microsoft/SmartKC-A-Smartphone-based-Corneal-Topographer/data/sample_images/kc_left.jpg

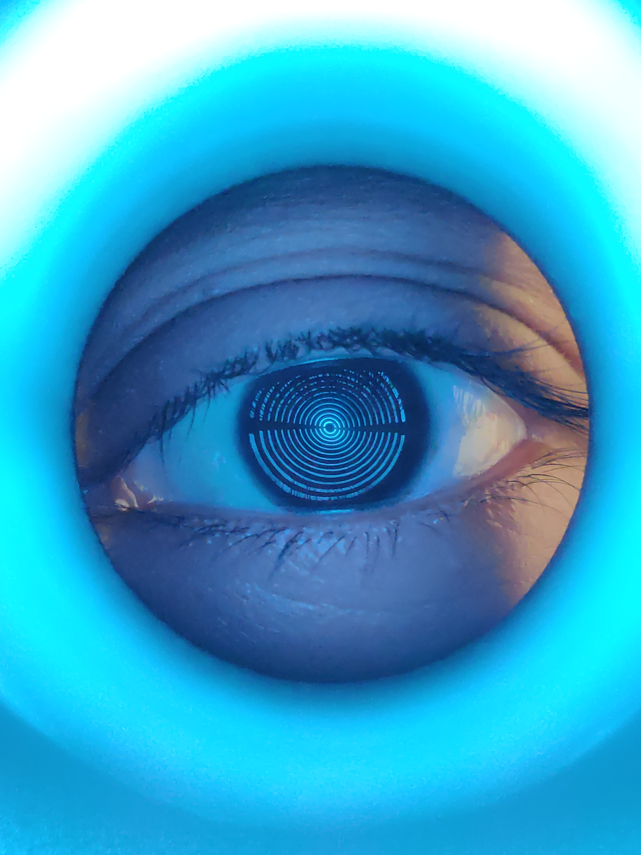
data/sample_images/kc_left.jpg
