microsoft/SmartKC-A-Smartphone-based-Corneal-Topographer/data/sample_images/kc_right.jpg

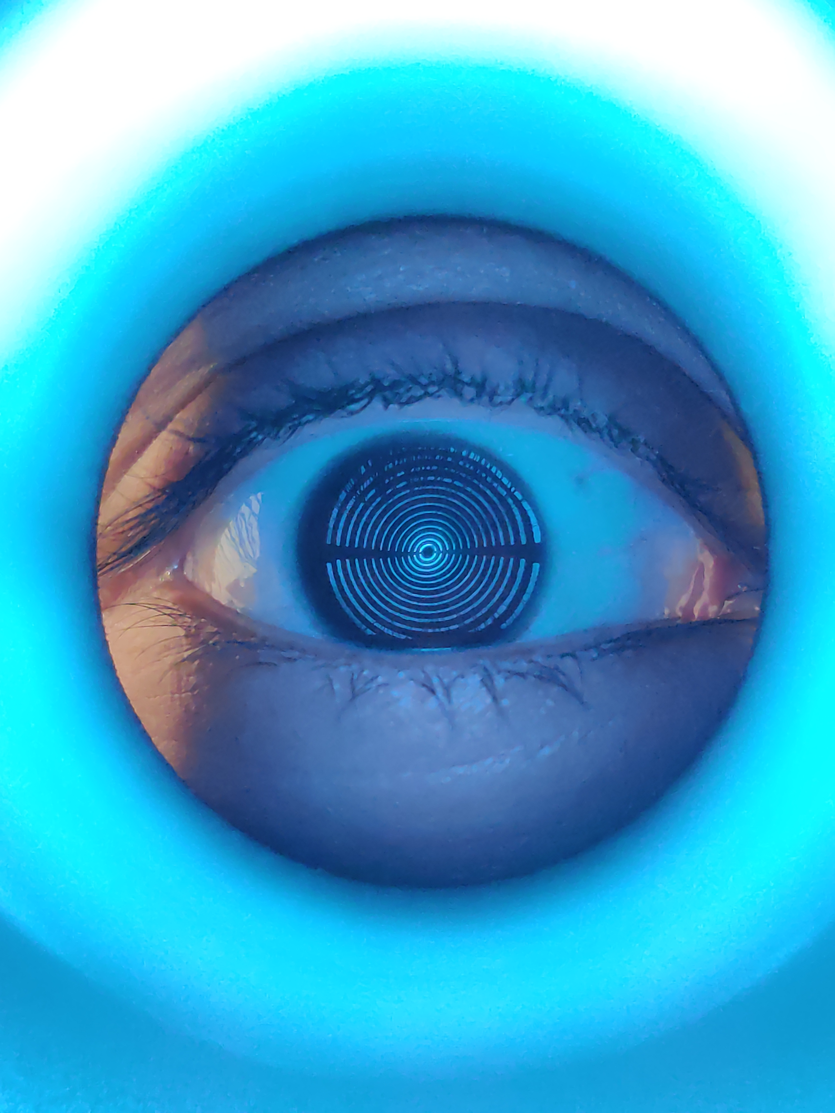
data/sample_images/kc_right.jpg
