microsoft/SmartKC-A-Smartphone-based-Corneal-Topographer/data/sample_images/nokc_left.jpg

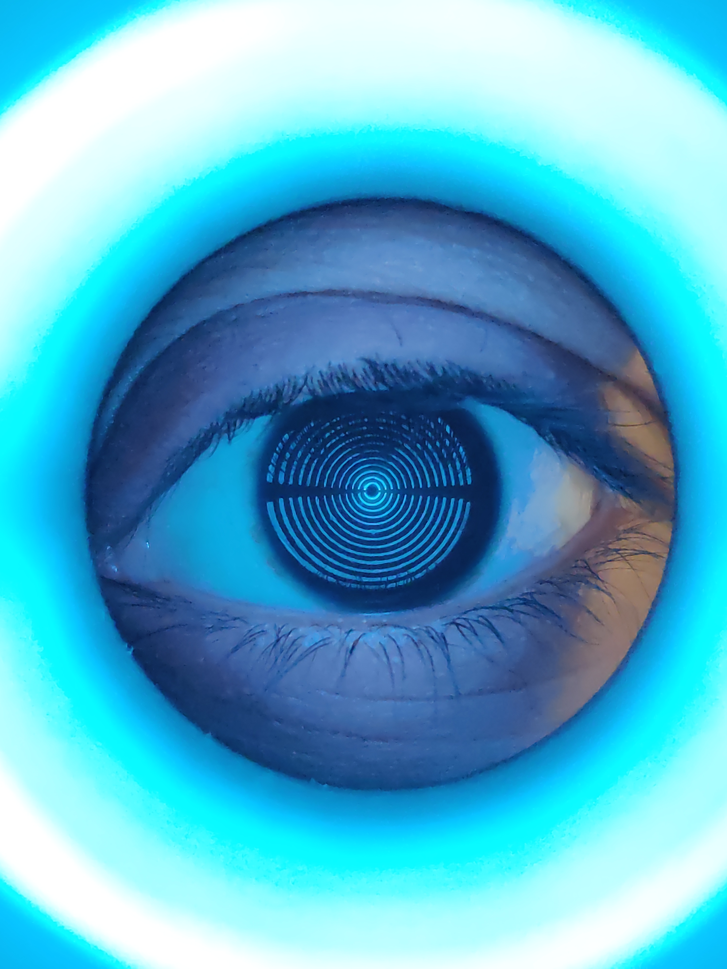
data/sample_images/nokc_left.jpg
