microsoft/SmartKC-A-Smartphone-based-Corneal-Topographer/data/sample_images/nokc_right.jpg

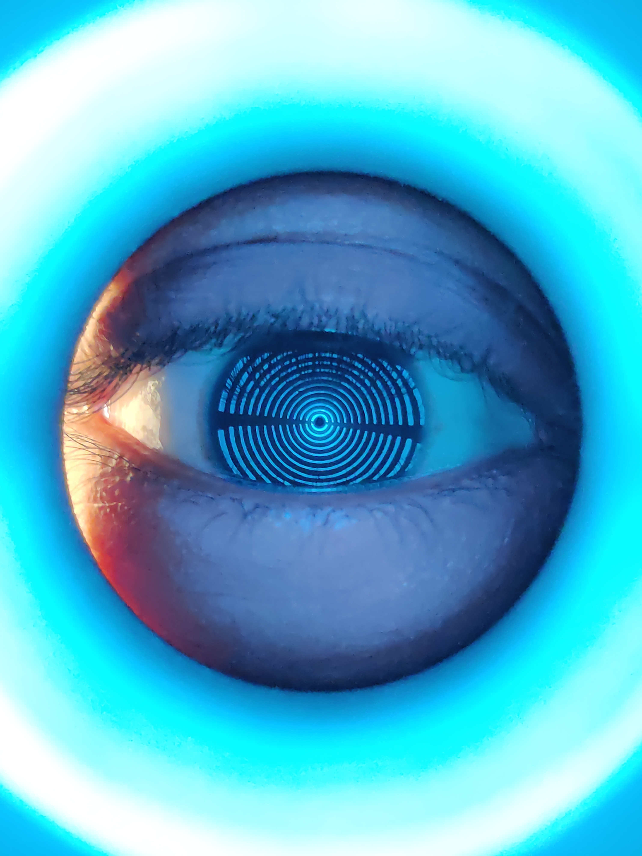
data/sample_images/nokc_right.jpg
