microsoft/SmartKC-A-Smartphone-based-Corneal-Topographer/data/sample_images_results/kc_left/kc_left_axialmap.png

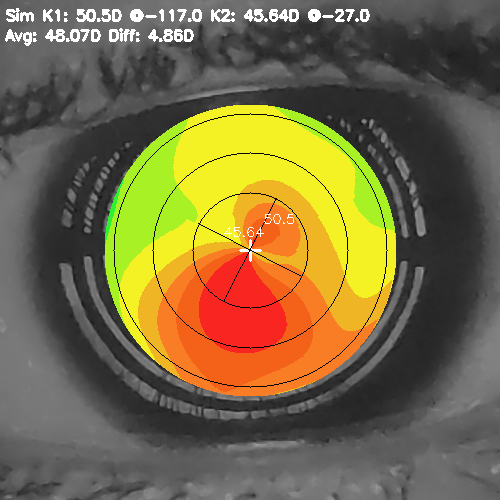
data/sample_images_results/kc_left/kc_left_axialmap.png
