microsoft/SmartKC-A-Smartphone-based-Corneal-Topographer/data/sample_images_results/kc_right/kc_right_tanmap.png

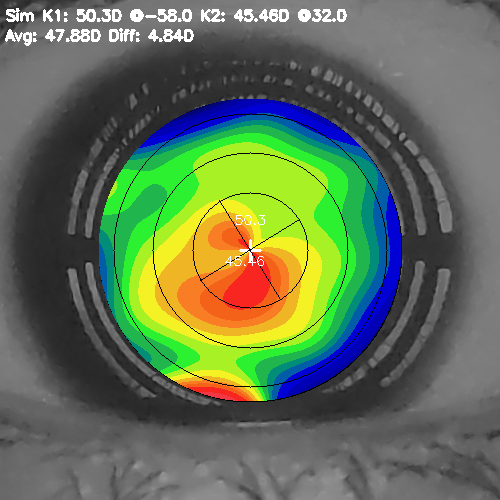
data/sample_images_results/kc_right/kc_right_tanmap.png
