microsoft/SmartKC-A-Smartphone-based-Corneal-Topographer/data/sample_images_results/nokc_left/nokc_left_axialmap.png

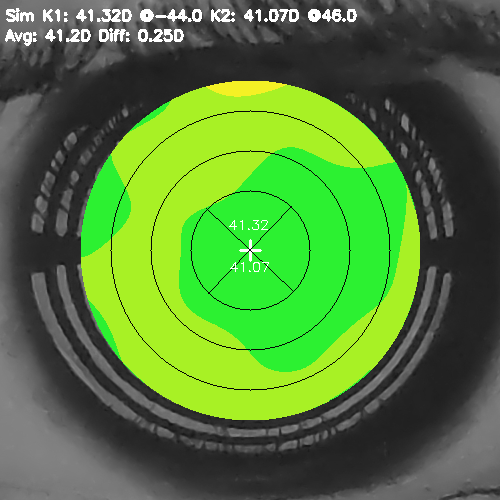
data/sample_images_results/nokc_left/nokc_left_axialmap.png
