microsoft/SmartKC-A-Smartphone-based-Corneal-Topographer/data/sample_images_results/nokc_right/nokc_right_tanmap.png

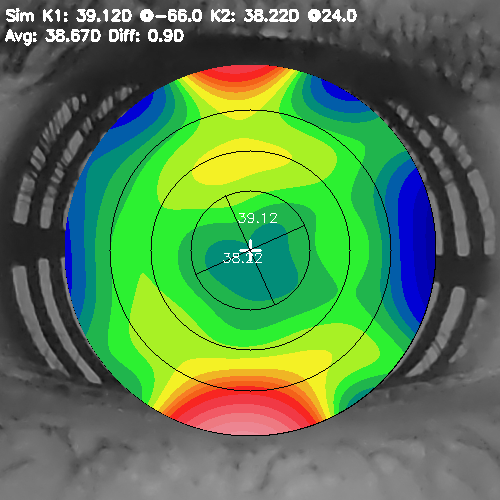
data/sample_images_results/nokc_right/nokc_right_tanmap.png
